SARAI-Lab-KIT/MOSAIC/hardware/STL-files/Access_Panel_1.stl

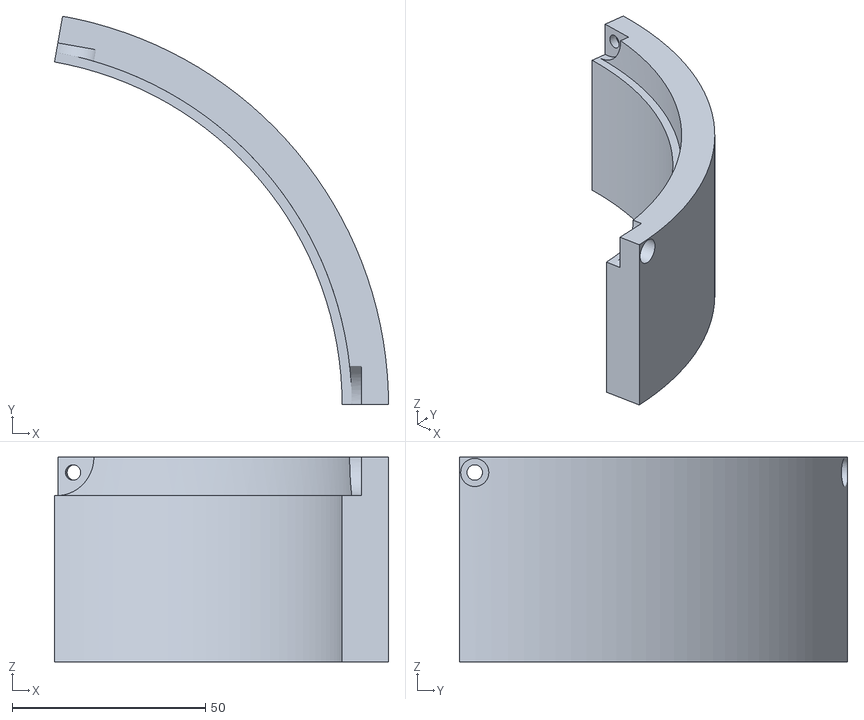
[picture p16: CAD file, 2026-03-30]
hardware/STL-files/Access_Panel_1.stl
86.4 x 100.5 x 53.0
